SunritHazra/HackroDevX/Gallery/45° View.png

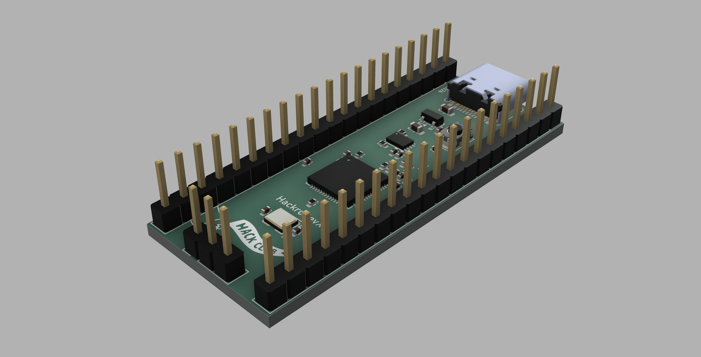
Gallery/45° View.png
