SunritHazra/HackroDevX/Gallery/KiCad PCB Render.png

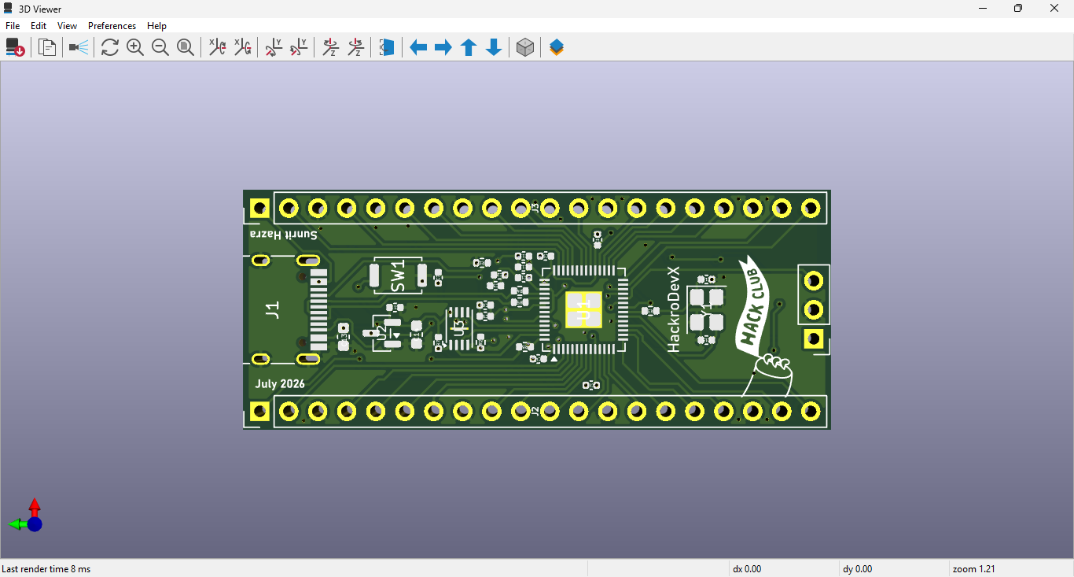
Gallery/KiCad PCB Render.png
