SunritHazra/HackroDevX/Gallery/JLCPCB BOM.png

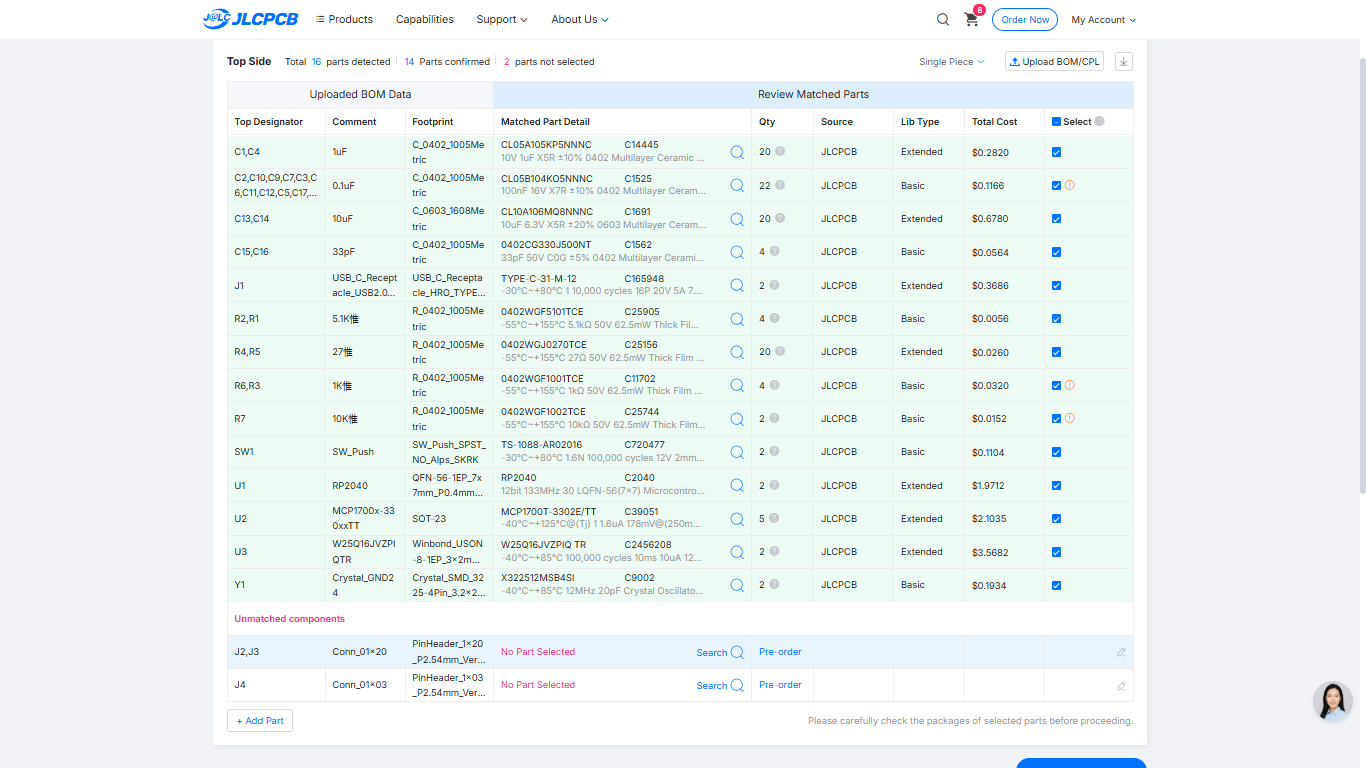
Gallery/JLCPCB BOM.png
