SunritHazra/HackroDevX/Gallery/JLCPCB Order.png

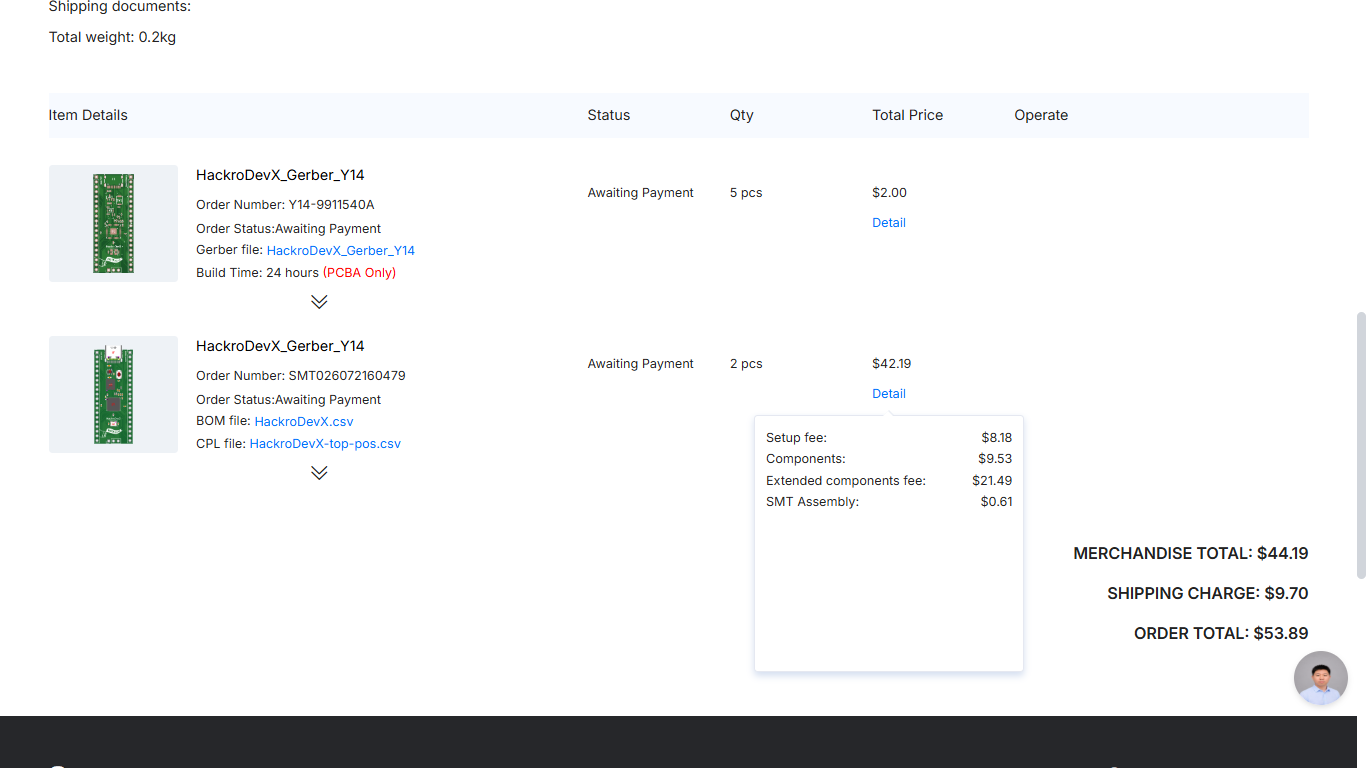
Gallery/JLCPCB Order.png
